pietervdvn/Luchtlichtje/v0.2/Firmware/WifiMinimal/WifiMinimal.ino

/*
    HTTP over TLS (HTTPS) example sketch

    This example demonstrates how to use
    WiFiClientSecure class to access HTTPS API.
    We fetch and display the status of
    esp8266/Arduino project continuous integration
    build.

    Limitations:
      only RSA certificates
      no support of Perfect Forward Secrecy (PFS)
      TLSv1.2 is supported since version 2.4.0-rc1

    Created by Ivan Grokhotkov, 2015.
    This example is in public domain.
*/

#include <ESP8266WiFi.h>
#include <WiFiClientSecure.h>

#ifndef STASSID
#define STASSID "Wireless Belgie"
#define STAPSK  ""
#endif

const char* ssid = STASSID;
const char* password = STAPSK;

const char* host = "data.sensor.community";
const char* sensor = "/airrohr/v1/sensor/7245/";
const int httpsPort = 443;

// Use web browser to view and copy
// SHA1 fingerprint of the certificate
const char fingerprint[] PROGMEM = "DF:14:13:1B:DF:BD:6E:DA:54:57:5C:41:E7:B4:FE:7F:40:B7:F9:84";

void setup() {
  Serial.begin(115200);
  Serial.println();
  Serial.print("connecting to ");
  Serial.println(ssid);
  WiFi.mode(WIFI_STA);
  WiFi.begin(ssid, password);
  while (WiFi.status() != WL_CONNECTED) {
    delay(500);
    Serial.print(".");
  }
  
}

void loop() {
    delay(1000);
    Serial.println("");
  Serial.println("WiFi connected");
  Serial.println("IP address: ");
  Serial.println(WiFi.localIP());


  

}
