pietervdvn/Luchtlichtje/v0.2/Firmware/LuchtLichtje/Assets.ino

// All assets are saved here
String logo = "<?xml version=\"1.0\" encoding=\"UTF-8\" standalone=\"no\"?>\n<!-- Created with Inkscape (http://www.inkscape.org/) -->\n\n<svg\n   width=\"76.729156mm\"\n   height=\"190.5mm\"\n   viewBox=\"0 0 76.729156 190.5\"\n   version=\"1.1\"\n   id=\"svg7938\"\n   inkscape:version=\"1.2.1 (9c6d41e410, 2022-07-14)\"\n   sodipodi:docname=\"Segnale stradale italiano - lanterne semaforiche per velocipedi (figura II 456 - riproduzione fotografica).svg\"\n   xmlns:inkscape=\"http://www.inkscape.org/namespaces/inkscape\"\n   xmlns:sodipodi=\"http://sodipodi.sourceforge.net/DTD/sodipodi-0.dtd\"\n   xmlns=\"http://www.w3.org/2000/svg\"\n   xmlns:svg=\"http://www.w3.org/2000/svg\">\n  <sodipodi:namedview\n     id=\"namedview7940\"\n     pagecolor=\"#ffffff\"\n     bordercolor=\"#000000\"\n     borderopacity=\"0.25\"\n     inkscape:showpageshadow=\"2\"\n     inkscape:pageopacity=\"0.0\"\n     inkscape:pagecheckerboard=\"0\"\n     inkscape:deskcolor=\"#d1d1d1\"\n     inkscape:document-units=\"mm\"\n     showgrid=\"false\"\n     inkscape:zoom=\"0.76257015\"\n     inkscape:cx=\"400.61888\"\n     inkscape:cy=\"50.487159\"\n     inkscape:window-width=\"1920\"\n     inkscape:window-height=\"991\"\n     inkscape:window-x=\"-9\"\n     inkscape:window-y=\"-9\"\n     inkscape:window-maximized=\"1\"\n     inkscape:current-layer=\"layer1\" />\n  <defs\n     id=\"defs7935\" />\n  <g\n     inkscape:label=\"Livello 1\"\n     inkscape:groupmode=\"layer\"\n     id=\"layer1\"\n     transform=\"translate(0.54568671,28.97997)\">\n    <g\n       id=\"g3311\"\n       transform=\"translate(-1430.4268,-15178.026)\">\n      <rect\n         style=\"fill:#ffffff;fill-rule:evenodd;stroke:#000000;stroke-width:1.05833;paint-order:markers fill stroke\"\n         id=\"rect36686-5-3-2-2\"\n         width=\"75.67083\"\n         height=\"189.44167\"\n         x=\"1430.4103\"\n         y=\"15149.575\" />\n      <g\n         id=\"g3085\"\n         transform=\"translate(172.68208,-76.926991)\">\n        <circle\n           style=\"fill:#000000;fill-rule:evenodd;stroke-width:0.722612;paint-order:markers fill stroke\"\n           id=\"path10991-3\"\n           cx=\"1295.5636\"\n           cy=\"15382.084\"\n           r=\"26.458334\" />\n        <path\n           id=\"path5866-0-6-6-0-5\"\n           style=\"color:#000000;fill:#27884d;fill-rule:evenodd;stroke-width:1.11223;paint-order:markers fill stroke\"\n           d=\"m 1289.733,15370.785 c -0.765,0 -1.4356,0.338 -1.7978,0.88 -0.3621,0.542 -0.3967,1.266 -0.072,1.859 0.2527,0.459 0.4949,0.675 0.5197,0.73 0.025,0.05 0.095,0.06 -0.2183,0.567 l -0.01,0.01 -2.497,4.367 c -0.9969,-0.489 -2.1178,-0.765 -3.3024,-0.765 -4.1255,0 -7.487,3.332 -7.487,7.421 0,4.089 3.3615,7.42 7.487,7.42 4.1256,0 7.4841,-3.331 7.4841,-7.42 0,-2.392 -1.1489,-4.524 -2.9277,-5.881 l 0.9578,-1.675 8.1642,6.294 c -0.073,0.261 -0.1184,0.583 -0.1184,0.98 0,2.355 2.12,2.032 2.12,2.032 l 4.8393,-0.451 c 0.622,3.472 3.6933,6.121 7.372,6.121 4.1257,0 7.4842,-3.331 7.4842,-7.42 0,-4.089 -3.3585,-7.421 -7.4842,-7.421 -1.1094,0 -2.1635,0.242 -3.1118,0.674 l -2.2758,-3.319 1.3324,-2.348 0.8267,0.184 c 0.7363,0.182 1.0381,-0.04 1.0324,-0.275 v -1.065 c 0,-0.456 -0.085,-0.619 -1.0242,-0.619 h -3.7729 c -0.4814,0 -0.924,0.69 0,1.13 l 1.4301,0.314 -1.3111,2.311 h -13.8546 c 0.3549,-0.651 0.421,-1.286 0.2171,-1.749 -0.2218,-0.506 -0.4984,-0.704 -0.5761,-0.846 -0.079,-0.143 -0.064,-0.247 0.01,-0.348 0.069,-0.103 0.2097,-0.226 0.567,-0.226 h 3.677 c 0,0 0.8273,0.06 0.8273,-0.732 0,-0.789 -0.8273,-0.734 -0.8273,-0.734 z m -1.0524,6.1 h 13.8625 l -3.7811,6.663 -1.2891,-0.04 c 0,0 -0.1796,-0.04 -0.4163,0.01 l -8.4477,-6.513 z m 15.3712,0.33 1.8069,2.634 c -1.3012,0.938 -2.2883,2.28 -2.7701,3.838 l -2.662,-0.09 z m -21.6937,2.683 c 0.9227,0 1.7951,0.205 2.575,0.571 l -2.4907,4.355 c -0.5862,0.108 -1.0117,0.613 -1.0121,1.204 10e-5,0.677 0.5536,1.226 1.2367,1.226 0.6831,0 1.2371,-0.548 1.2371,-1.226 10e-5,-0.192 -0.046,-0.382 -0.1345,-0.557 l 2.4122,-4.217 c 1.3349,1.092 2.1835,2.744 2.1835,4.601 0,3.296 -2.6804,5.952 -6.0072,5.952 -3.3267,0 -6.0072,-2.656 -6.0072,-5.952 0,-3.299 2.6805,-5.957 6.0072,-5.957 z m 27.8913,0 c 3.3267,0 6.0073,2.658 6.0073,5.957 0,3.296 -2.6806,5.952 -6.0073,5.952 -2.9257,0 -5.353,-2.054 -5.8957,-4.792 l 6.4408,-0.601 c 1.2884,-0.199 1.5021,-2.323 -0.2119,-2.486 h -0.142 l -2.4607,-3.588 c 0.6998,-0.282 1.466,-0.439 2.2695,-0.439 z m -3.5639,1.156 1.9283,2.811 -3.9848,-0.129 c 0.4132,-1.08 1.1334,-2.008 2.0565,-2.682 z\" />\n      </g>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

String wifiselect = "<!DOCTYPE html>\n<html lang=\"en\">\n<head>\n    <meta charset=\"UTF-8\">\n    <meta name=\"viewport\" content=\"width=device-width, initial-scale=1.0\">\n    <link rel=\"icon\" type=\"image/svg\" href=\"./logo.svge\"/>\n    <link rel=\"manifest\" href=\"./manifest.webmanifest\">\n    <title>Traffic Light Controller</title>\n    <style>        .slidecontainer {\n        width: 100%;\n    }\n\n    body {\n        background: black;\n        color: cyan;\n        font-family: monospace;\n        font-size: large\n    }\n    </style>\n</head>\n<body>\n<div class=\"slidecontainer\">\n    <label for=\"ssid\">Wifi network name</label><input type=\"text\" id=\"ssid\" name=\"ssid\">\n    <br/>\n    <label for=\"password\">Wifi password</label><input id=\"password\" name=\"password\" type=\"password\">\n    <br/>\n    <label for=\"ssid_2\">Fallback Wifi network name</label><input type=\"text\" id=\"ssid_2\" name=\"ssid\">\n    <br/>\n    <label for=\"password_2\">Fallback Wifi password</label><input id=\"password_2\" name=\"password\" type=\"password\">\n    <br/>\n    <label for=\"hostname\">Hostname (the device will be visible as hostname.local)</label><input type=\"text\" id=\"hostname\" name=\"hostname\" value=\"luchtlichtje\" >\n    <br/>\n    <button type=\"button\" id=\"apply\">Apply</button>\n    <script>\n\n        const ssid = document.getElementById(\"ssid\");\n        const password = document.getElementById(\"password\");\n        const ssid_2 = document.getElementById(\"ssid_2\");\n        const password_2 = document.getElementById(\"password_2\");\n        const hostname = document.getElementById(\"hostname\");\n        const apply = document.getElementById(\"apply\");\n        function configure() {\n            let query = `ssid=${ssid.value}&password=${password.value}&ssid_2=${ssid_2.value}&password_2=${password_2.value}&hostname=${hostname.value}`;\n            const xhr = new XMLHttpRequest();\n            xhr.open(\"GET\", `./configure?${query}`);\n            xhr.send();\n        }\n        apply.onclick = configure;\n    </script>\n</div>\n</body>\n</html>\n\n";

#if PEDESTRIAN_LIGHT
String landing = "<!DOCTYPE html>\n<html lang=\"en\">\n<head>\n    <meta charset=\"UTF-8\">\n    <meta name=\"viewport\" content=\"width=device-width, initial-scale=1.0\">\n    <link rel=\"icon\" type=\"image/svg\" href=\"./logo.svg\"/>\n    <link rel=\"manifest\" href=\"./manifest.webmanifest\">\n    <title>Luchtlichtje Controller</title>\n    <style>        .slidecontainer {\n        width: 100%;\n    }\n\n    body {\n        background: black;\n        color: cyan;\n        font-family: monospace;\n        font-size: large\n    }\n\n    </style>\n</head>\n<body>\n<div class=\"slidecontainer\">\n    <br/>\n\n    <label for=\"sensorid\">Sensor ID (must have a SDS11)</label><input type=\"text\" id=\"sensorid\" name=\"sensorid\">\n    <button id=\"apply_btn\">Apply</button>\n    <a href=\"setup\">Switch wifi network</a>\n\n    <script>\n        \n        let sensorfield = document.getElementById(\"sensorid\");\n\n        let updatePending = true; /* Perform an update on load to set the clock*/\n\n        function configure() {\n            if (!updatePending) {\n                return;\n            }\n            if(isNaN(Number(sensorfield.value)) ){\n                alert(\"Invalid number\")\n                return\n            }\n            updatePending = false;\n            let query = `sensor=${sensorfield.value}`;\n            const xhr = new XMLHttpRequest();\n            xhr.open(\"GET\", `./configure?${query}`);\n            xhr.send();\n        };\n        \n        function getIp() {\n            console.log(\"Fetching ip...\")\n            fetch(\"./status\").then((response) => {\n            response.json().then((status) => {\n            console.log(status);\n            sensorfield.value = \"\"+ status.sensorid;\n            const link = document.createElement(\"a\")\n            link.href = \"http://\"+status.ip\n            link.innerHTML = \"IP address is \"+status.ip\n            document.body.append(link)\n\n                const linkho = document.createElement(\"a\")\n                linkho.href = \"http://\"+status.hostname+\".local\"\n                linkho.innerHTML = \"Hostname is \"+status.hostname\n                document.body.append(linkho)\n            })\n            });\n        }\n        \n        getIp()\n\n        function update() {\n            updatePending = true;\n        };\n        const button = document.getElementById(\"apply_btn\");\n        button.onclick = update\n    </script>\n</div>\n</body>\n</html>\n\n";

#else
String landing = "<!DOCTYPE html>\n<html lang=\"en\">\n<head>\n    <meta charset=\"UTF-8\">\n    <meta name=\"viewport\" content=\"width=device-width, initial-scale=1.0\">\n    <link rel=\"icon\" type=\"image/svg\" href=\"./logo.svg\"/>\n    <link rel=\"manifest\" href=\"./manifest.webmanifest\">\n    <title>Luchtlichtje Controller</title>\n    <style>        .slidecontainer {\n        width: 100%;\n    }\n\n    body {\n        background: black;\n        color: cyan;\n        font-family: monospace;\n        font-size: large\n    }\n\n    </style>\n</head>\n<body>\n<div class=\"slidecontainer\">\n    <br/>\n\n    <label for=\"sensorid\">Sensor ID (must have a SDS11)</label><input type=\"text\" id=\"sensorid\" name=\"sensorid\">\n    <button id=\"apply_btn\">Apply</button>\n    <a href=\"setup\">Switch wifi network</a>\n\n    <script>\n        \n        let sensorfield = document.getElementById(\"sensorid\");\n\n        let updatePending = true; /* Perform an update on load to set the clock*/\n\n        function configure() {\n            if (!updatePending) {\n                return;\n            }\n            if(isNaN(Number(sensorfield.value)) ){\n                alert(\"Invalid number\")\n                return\n            }\n            updatePending = false;\n            let query = `sensor=${sensorfield.value}`;\n            const xhr = new XMLHttpRequest();\n            xhr.open(\"GET\", `./configure?${query}`);\n            xhr.send();\n        };\n        \n        function getIp() {\n            console.log(\"Fetching ip...\")\n            fetch(\"./status\").then((response) => {\n            response.json().then((status) => {\n            console.log(status);\n            sensorfield.value = \"\"+ status.sensorid;\n            const link = document.createElement(\"a\")\n            link.href = \"http://\"+status.ip\n            link.innerHTML = \"IP address is \"+status.ip\n            document.body.append(link)\n\n                const linkho = document.createElement(\"a\")\n                linkho.href = \"http://\"+status.hostname+\".local\"\n                linkho.innerHTML = \"Hostname is \"+status.hostname\n                document.body.append(linkho)\n            })\n            });\n        }\n        \n        getIp()\n\n        function update() {\n            updatePending = true;\n        };\n        const button = document.getElementById(\"apply_btn\");\n        button.onclick = update\n    </script>\n</div>\n</body>\n</html>\n\n";

#endif
